JD277/ADAKADEMY-WRO2025/src/UML_Diagram.png

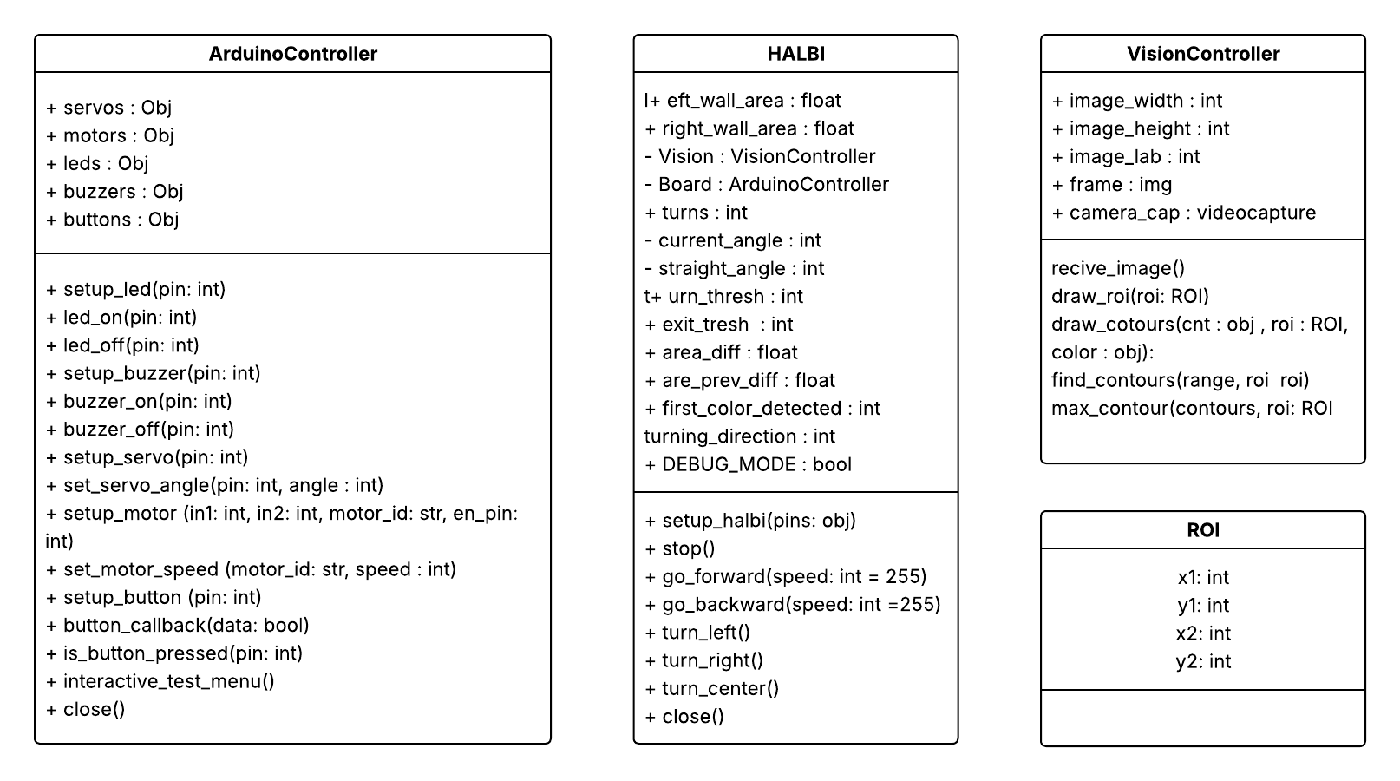
src/UML_Diagram.png
