JD277/ADAKADEMY-WRO2025/v-photos/back.jpg

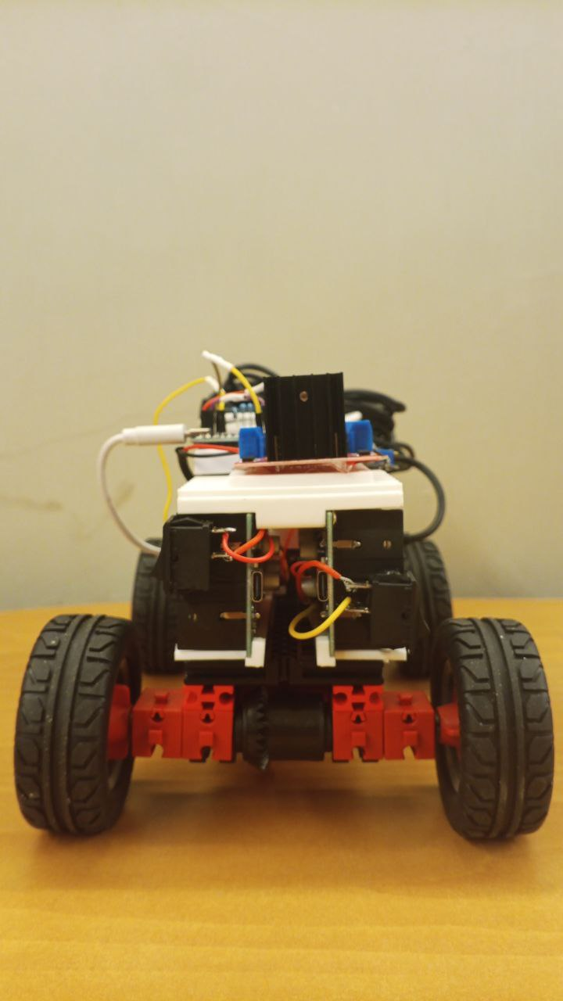
v-photos/back.jpg
